IlKaiser/IoT_Group-Project/imgs/2.png

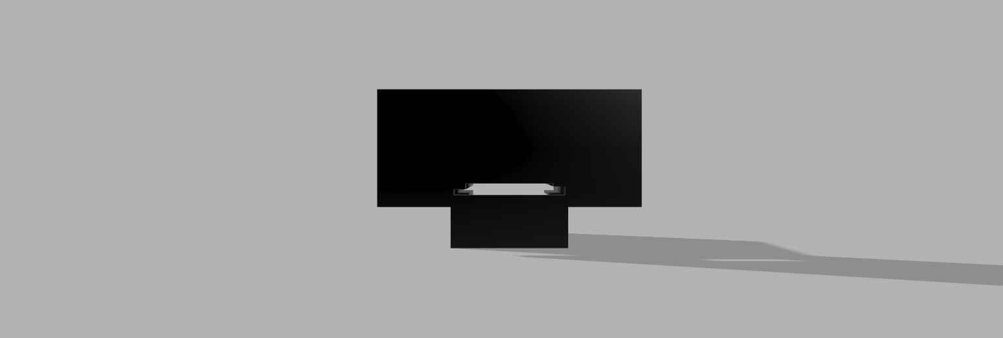
imgs/2.png
