IlKaiser/IoT_Group-Project/imgs/3.png

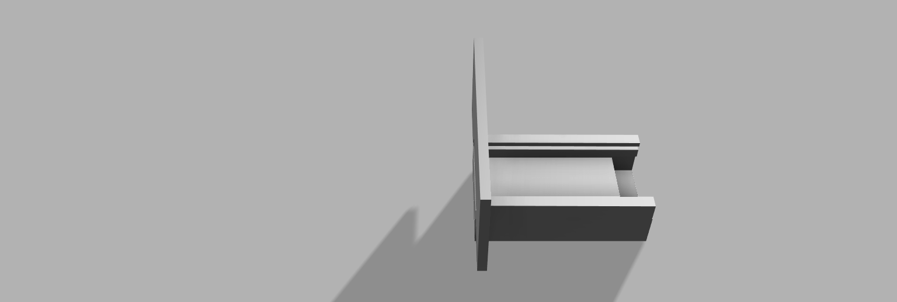
imgs/3.png
