IlKaiser/IoT_Group-Project/imgs/Curr_Floater_.png

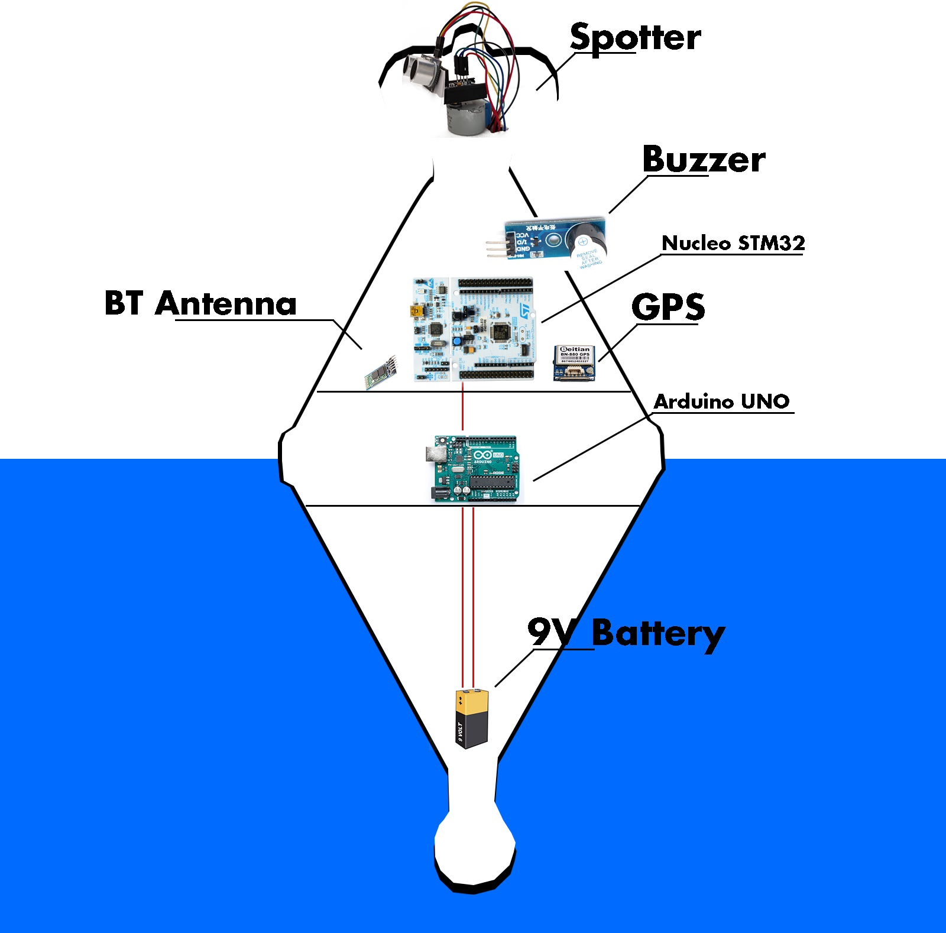
imgs/Curr_Floater_.png
