IlKaiser/IoT_Group-Project/imgs/Definitive_floater_.png

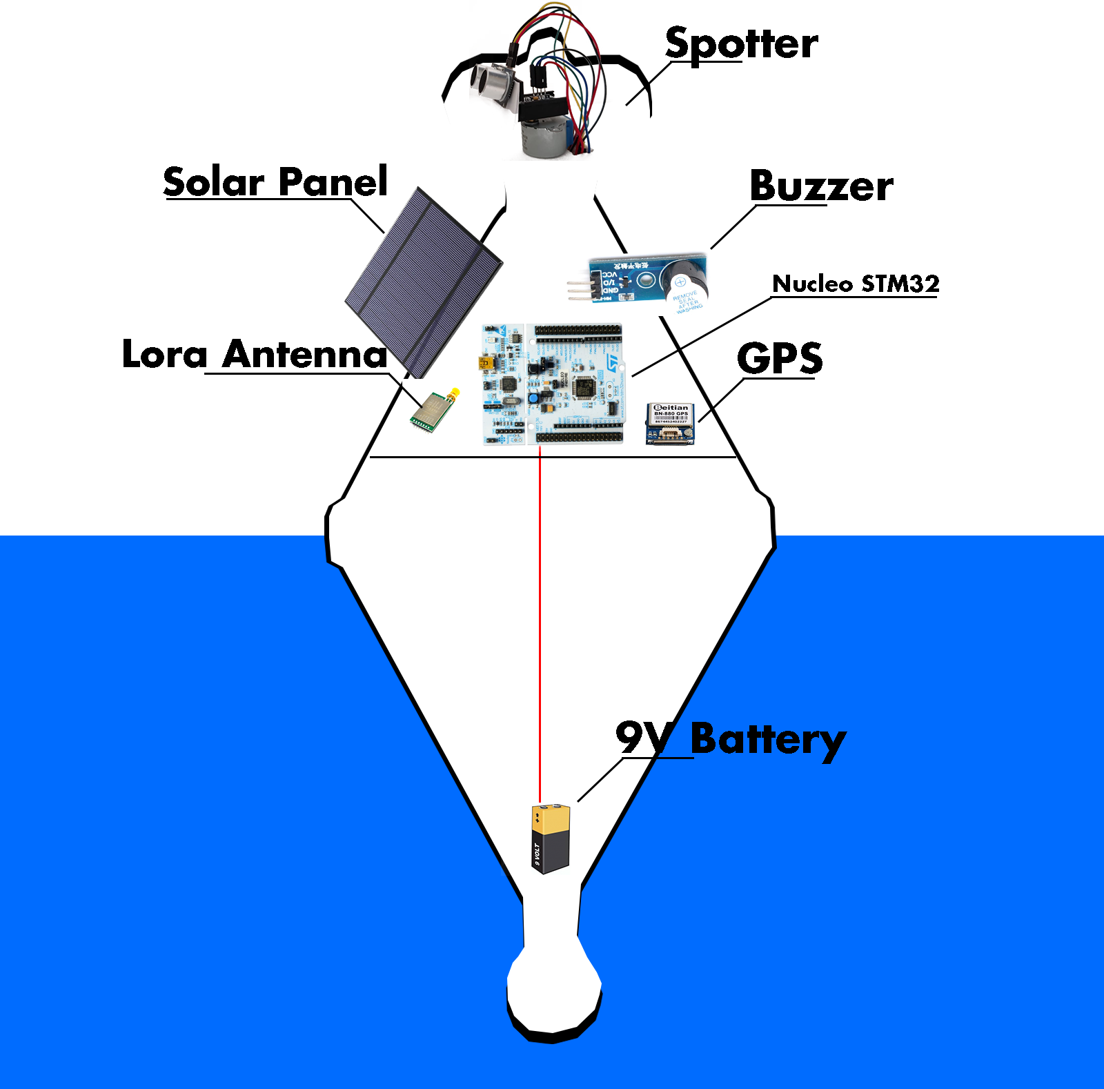
imgs/Definitive_floater_.png
