IlKaiser/IoT_Group-Project/imgs/SCHEMA.png

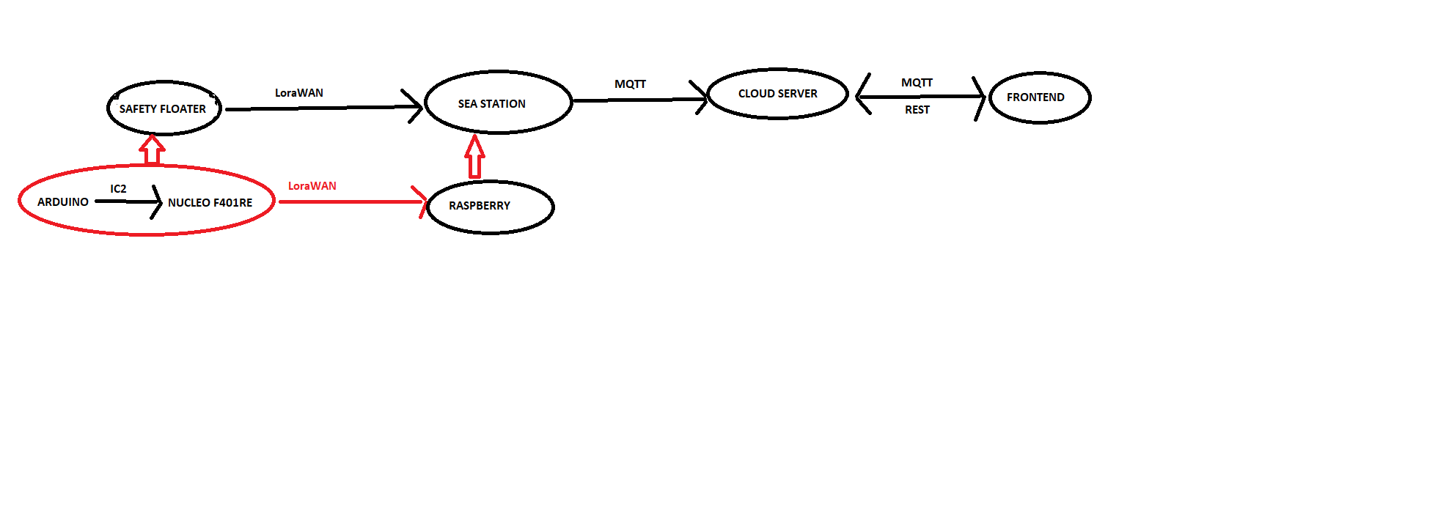
imgs/SCHEMA.png
