IlKaiser/IoT_Group-Project/imgs/Sea_Station.png

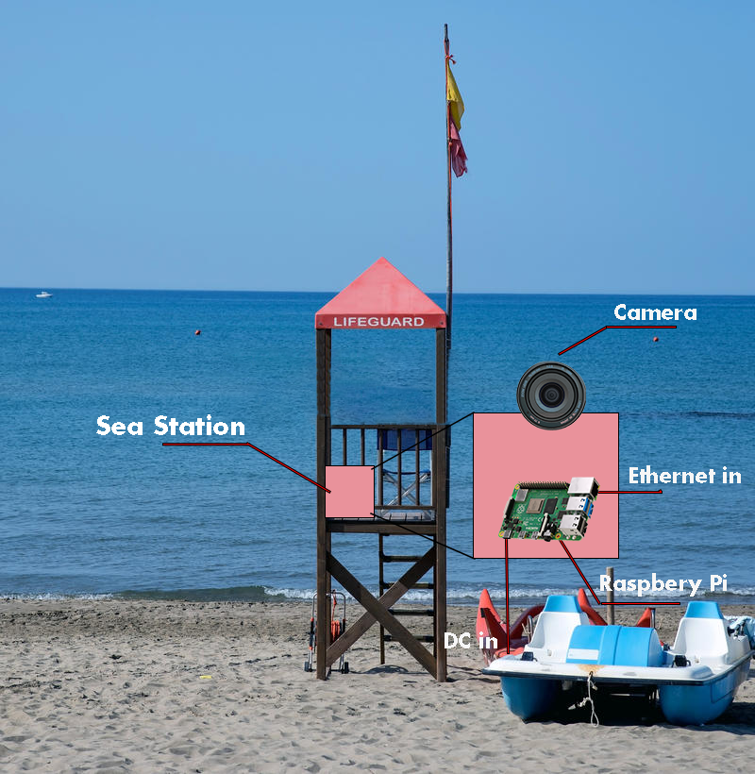
imgs/Sea_Station.png
