IlKaiser/IoT_Group-Project/imgs/SF.png

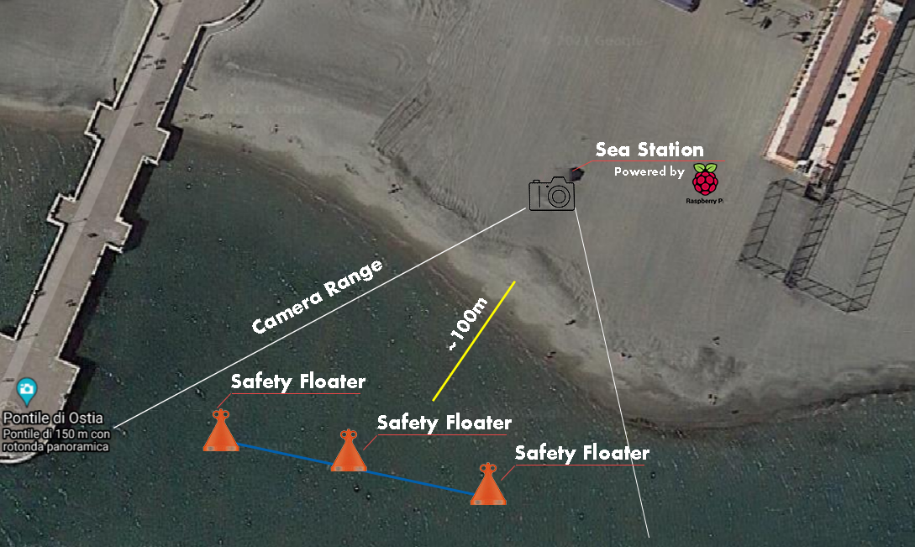
imgs/SF.png
