IlKaiser/IoT_Group-Project/imgs/violation_rule.png

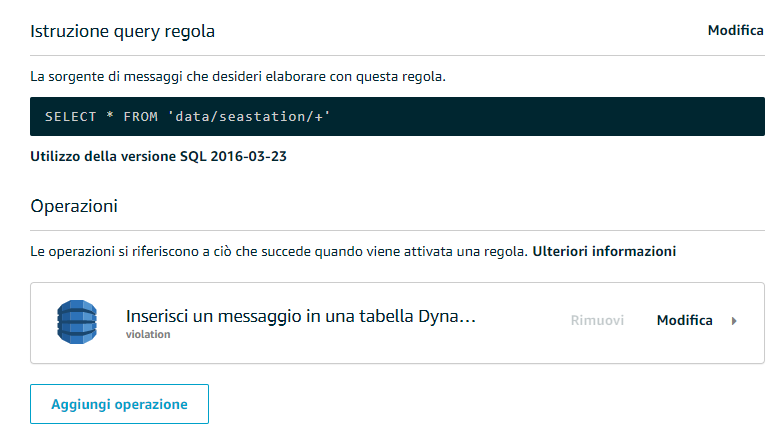
imgs/violation_rule.png
