IlKaiser/IoT_Group-Project/raspberry_code/tests/boat1.jpg

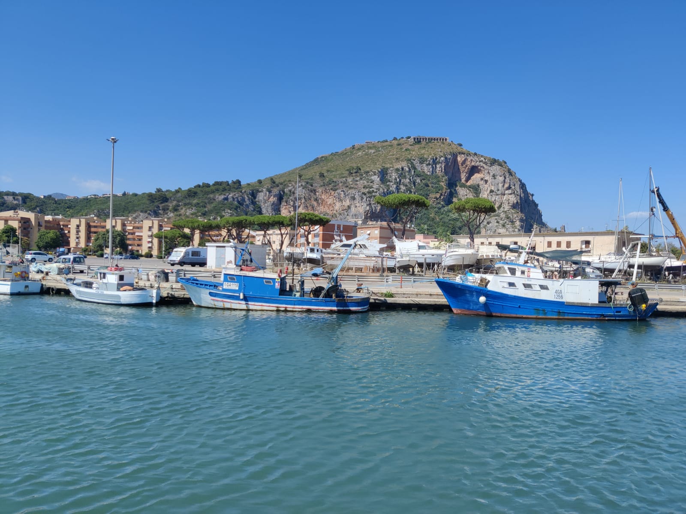
raspberry_code/tests/boat1.jpg
