IlKaiser/IoT_Group-Project/raspberry_code/tests/boat2.jpg

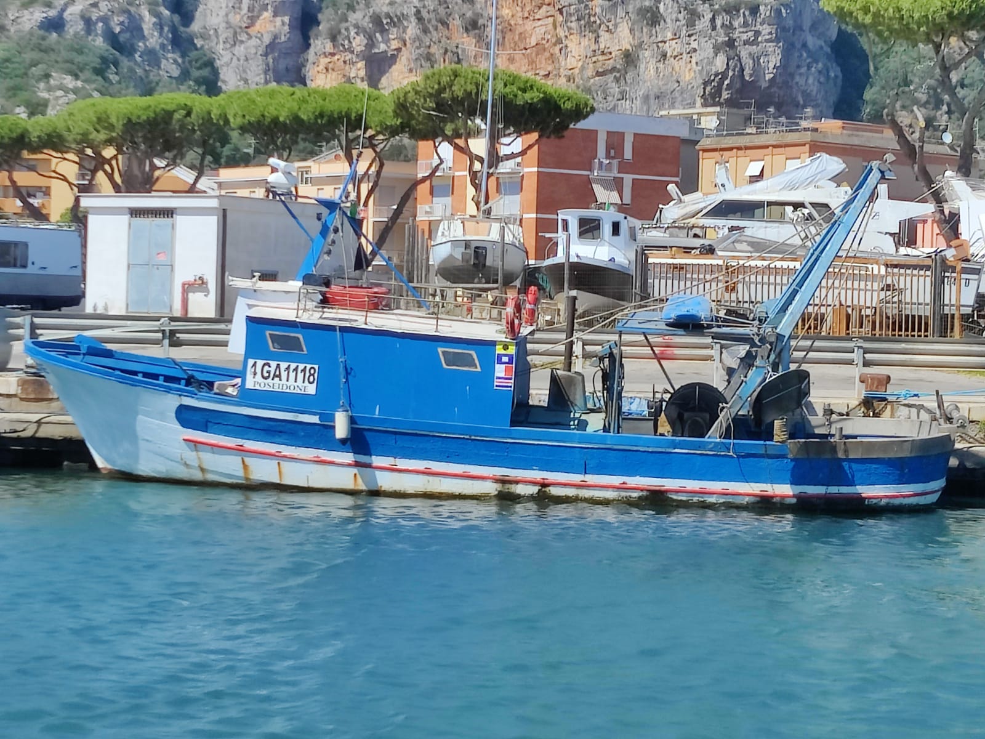
raspberry_code/tests/boat2.jpg
