IlKaiser/IoT_Group-Project/raspberry_code/tests/boat3.jpg

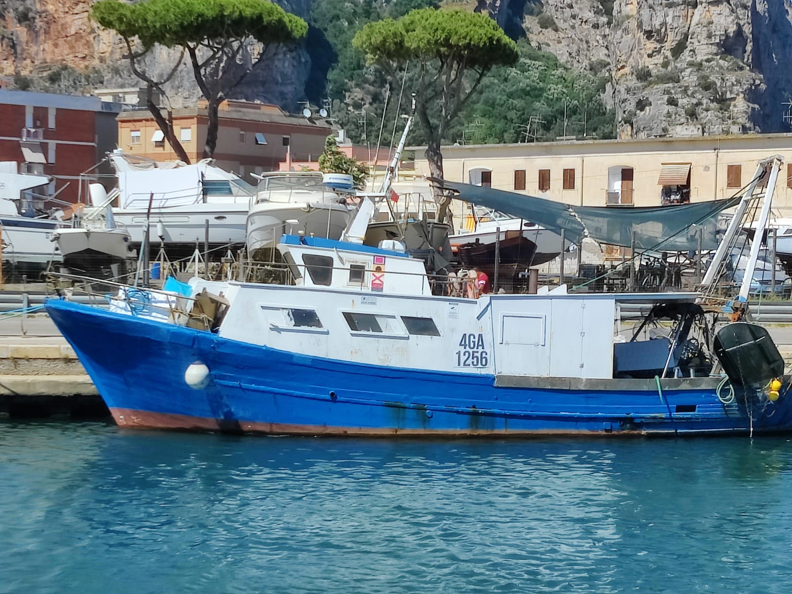
raspberry_code/tests/boat3.jpg
