IlKaiser/IoT_Group-Project/raspberry_code/tests/boat4.jpg

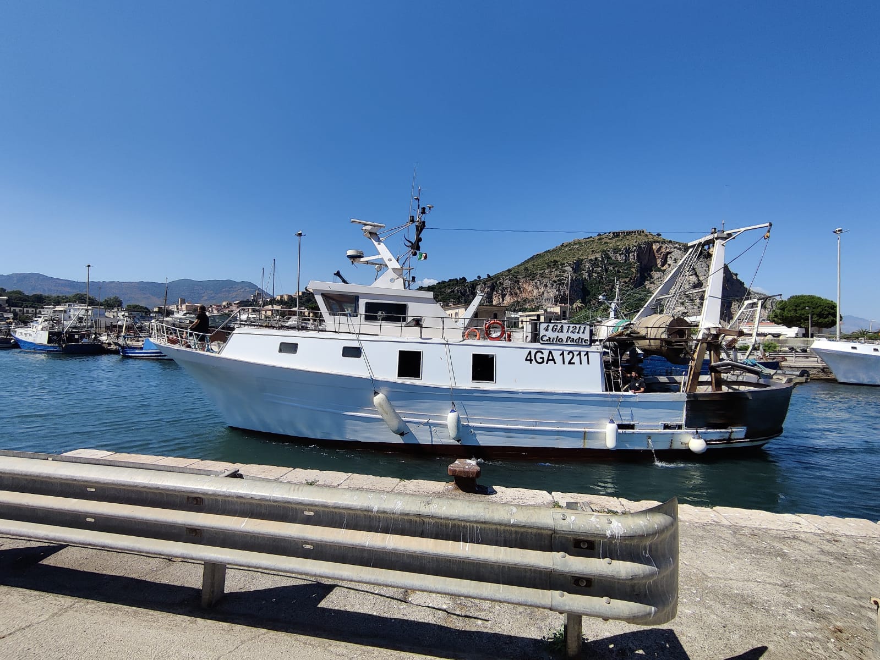
raspberry_code/tests/boat4.jpg
