IlKaiser/IoT_Group-Project/raspberry_code/tests/boat5.jpg

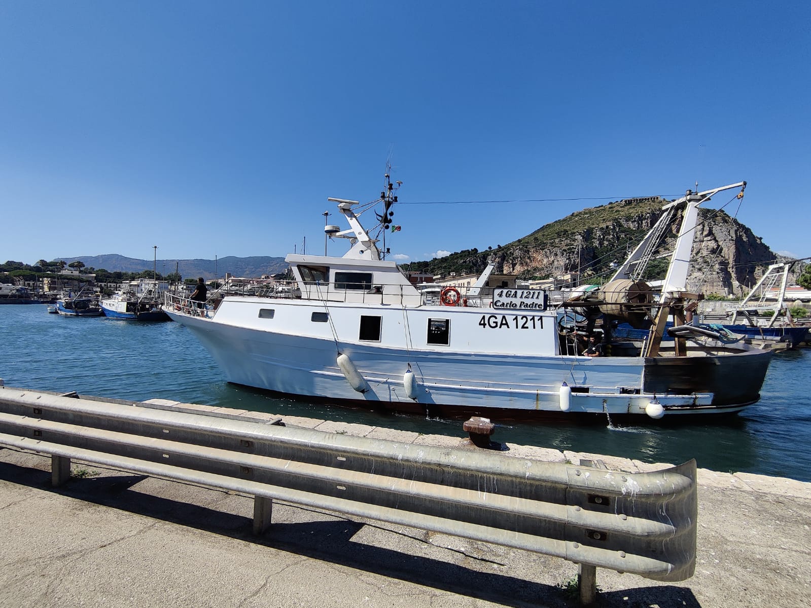
raspberry_code/tests/boat5.jpg
