IlKaiser/IoT_Group-Project/raspberry_code/tests/boat6.jpg

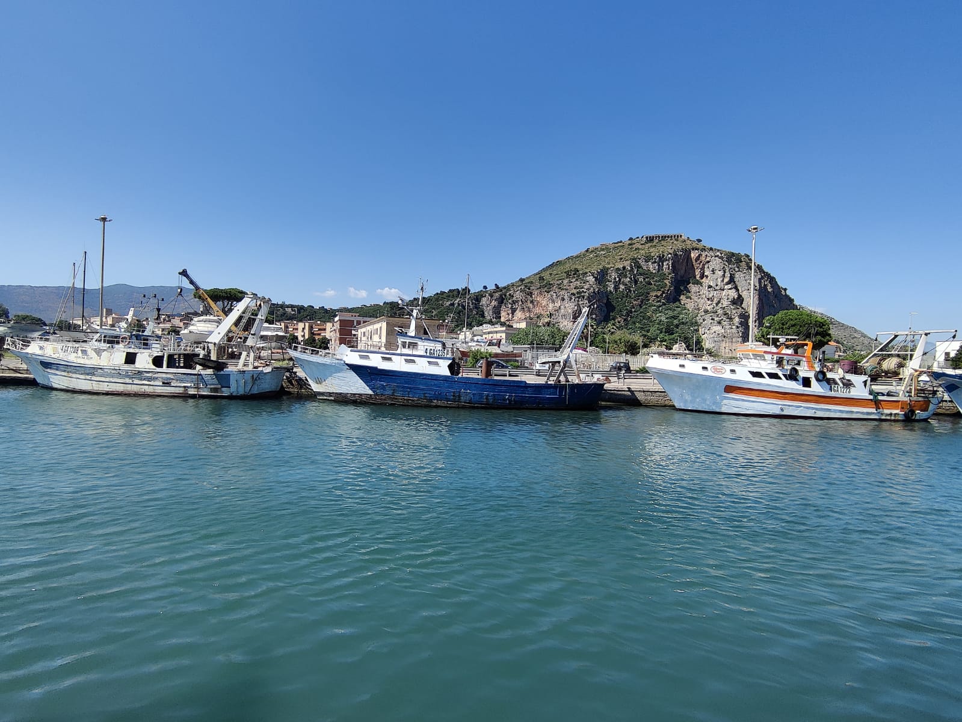
raspberry_code/tests/boat6.jpg
