IlKaiser/IoT_Group-Project/raspberry_code/tests/boat7.jpg

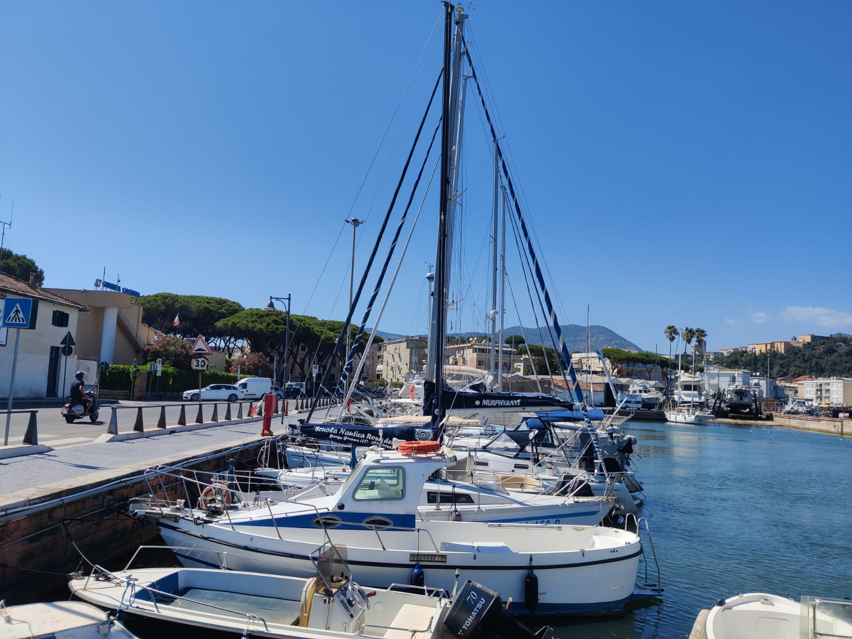
raspberry_code/tests/boat7.jpg
