IlKaiser/IoT_Group-Project/raspberry_code/tests/boat.jpg

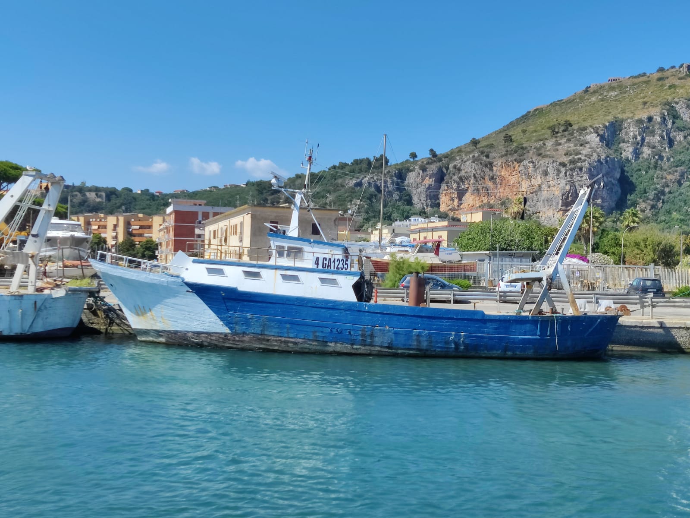
raspberry_code/tests/boat.jpg
