IlKaiser/IoT_Group-Project/raspberry_code/tests/sea3.jpg

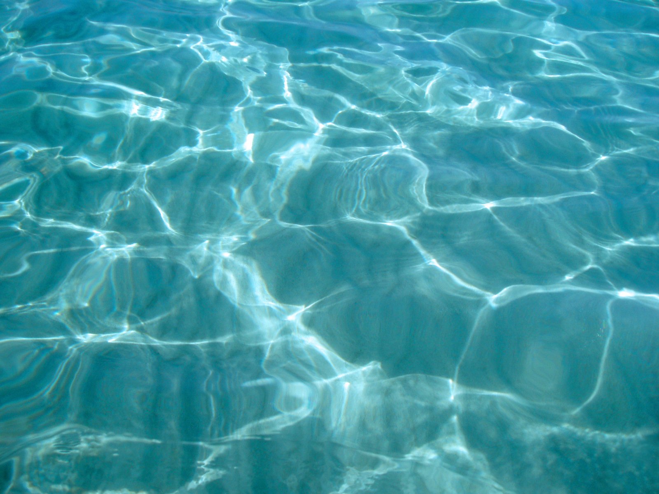
raspberry_code/tests/sea3.jpg
